SuperHouse/Testomatic/Images/Testomatic-PCB-annotated.jpeg

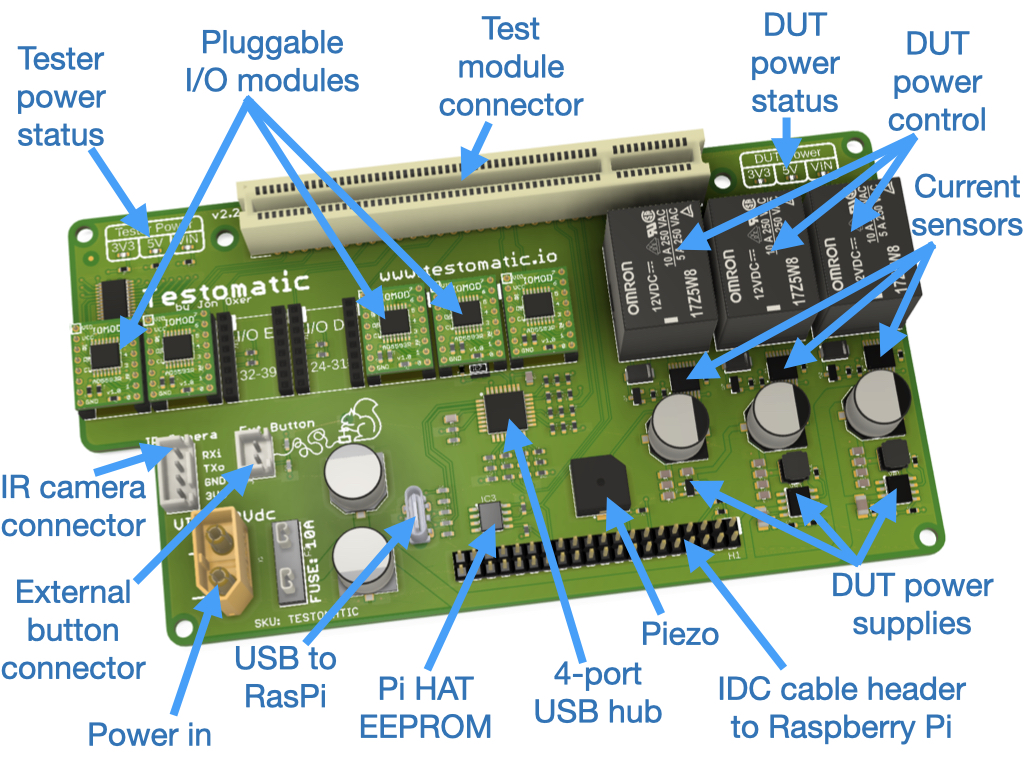
Images/Testomatic-PCB-annotated.jpeg
